Ukacha21/welstech/CAD/demo_big esp/61HXYjyJ1OL._AC_SL1001_.jpg

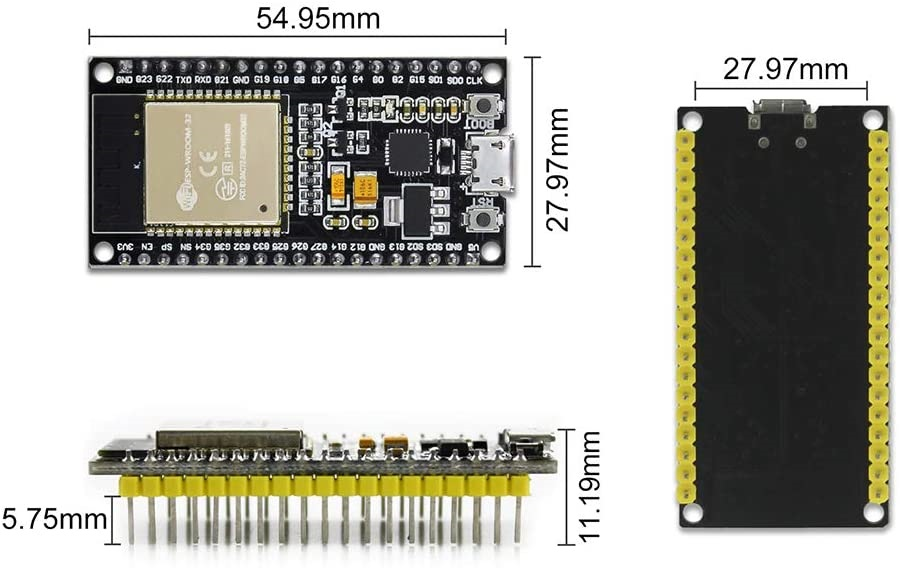
CAD/demo_big esp/61HXYjyJ1OL._AC_SL1001_.jpg
