Ukacha21/welstech/CAD/demo_big esp/bd75cf8a918120651273d0a94ace47d1c933943b_2_1024x606.png

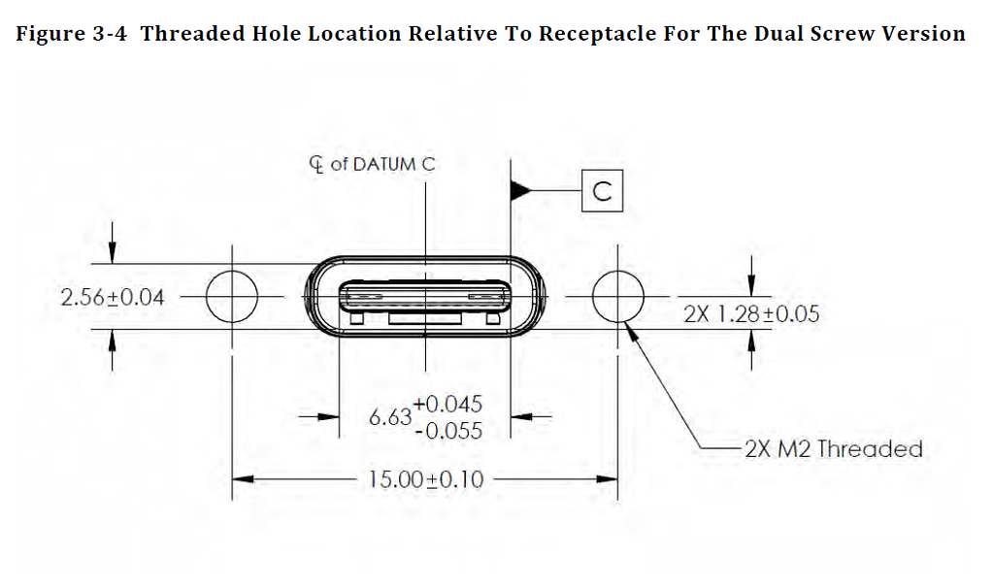
CAD/demo_big esp/bd75cf8a918120651273d0a94ace47d1c933943b_2_1024x606.png
