Ukacha21/welstech/CAD/demo_big esp/buttons3.jpg

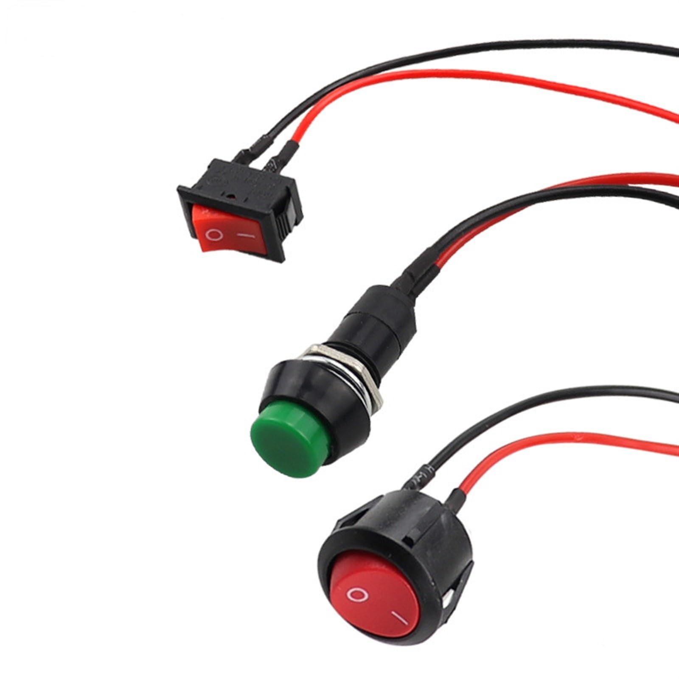
CAD/demo_big esp/buttons3.jpg
