Ukacha21/welstech/CAD/demo_big esp/buttons.png

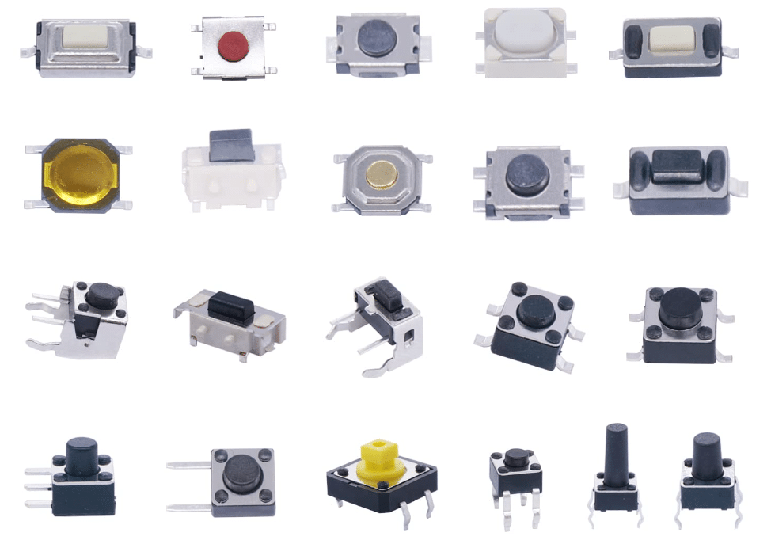
CAD/demo_big esp/buttons.png
