Ukacha21/welstech/CAD/demo_big esp/esp32 hd image.jpg

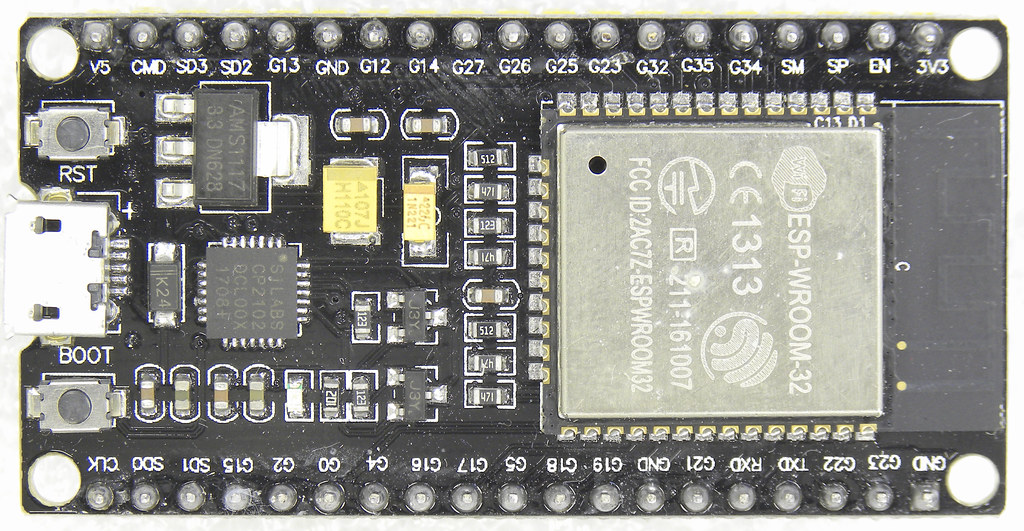
CAD/demo_big esp/esp32 hd image.jpg
