Ukacha21/welstech/CAD/demo_big esp/PAN-USB-C-SL-DIM1-500x500.webp

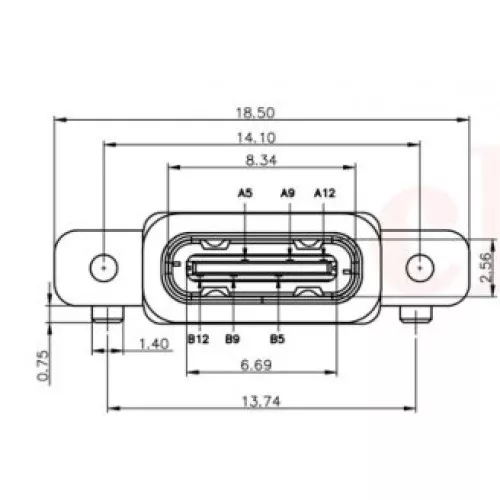
CAD/demo_big esp/PAN-USB-C-SL-DIM1-500x500.webp
