Ukacha21/welstech/Code/bpm formula.png

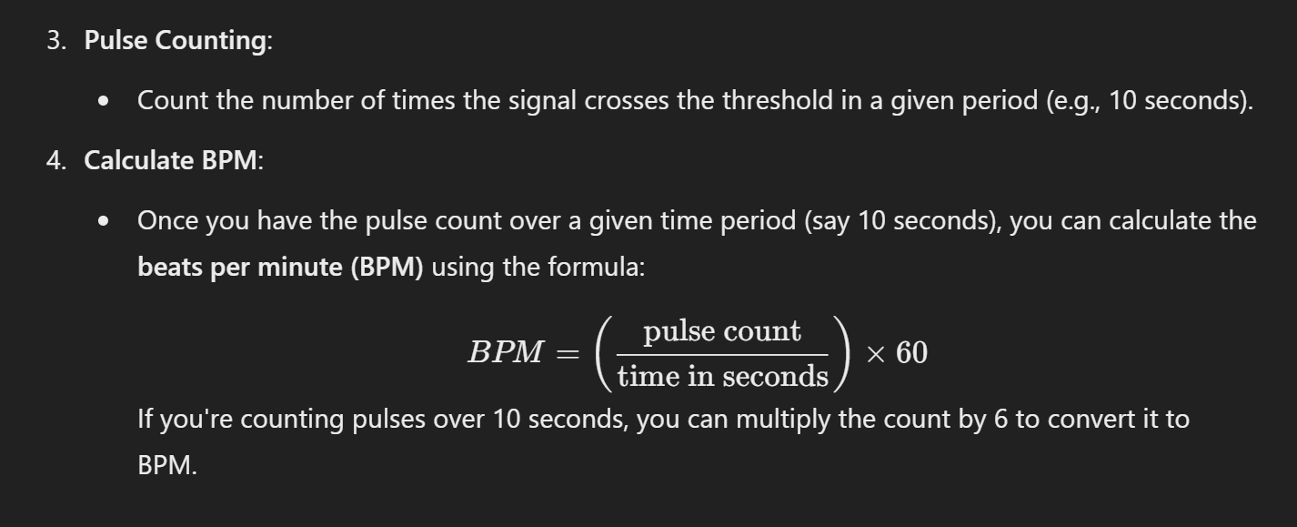
Code/bpm formula.png
