Ukacha21/welstech/Code/COM PORT name.png

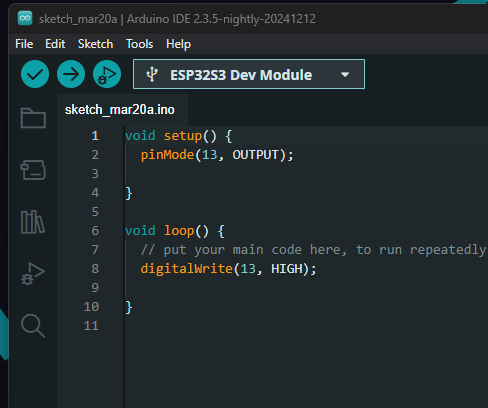
Code/COM PORT name.png
