Ukacha21/welstech/Schemaatics/BACKG.jpg

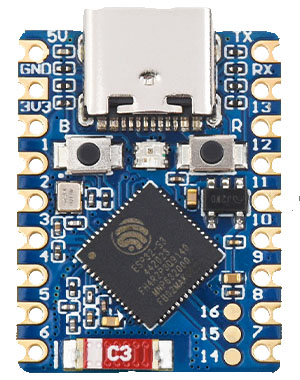
Schemaatics/BACKG.jpg
