Ukacha21/welstech/Schemaatics/breadboard dimensions.webp

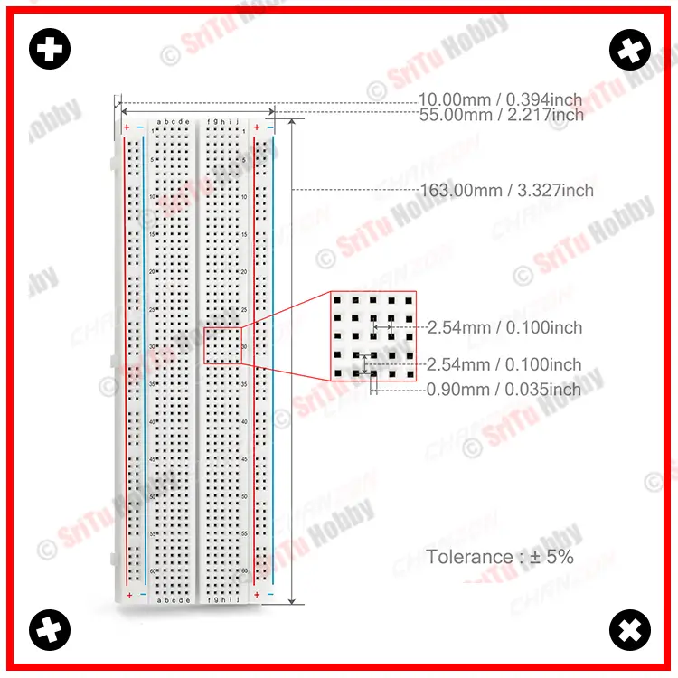
Schemaatics/breadboard dimensions.webp
