Ukacha21/welstech/Schemaatics/esp32-s3-mini-from-3-3v-source-v0-9cdqbcgkuqyc1.png

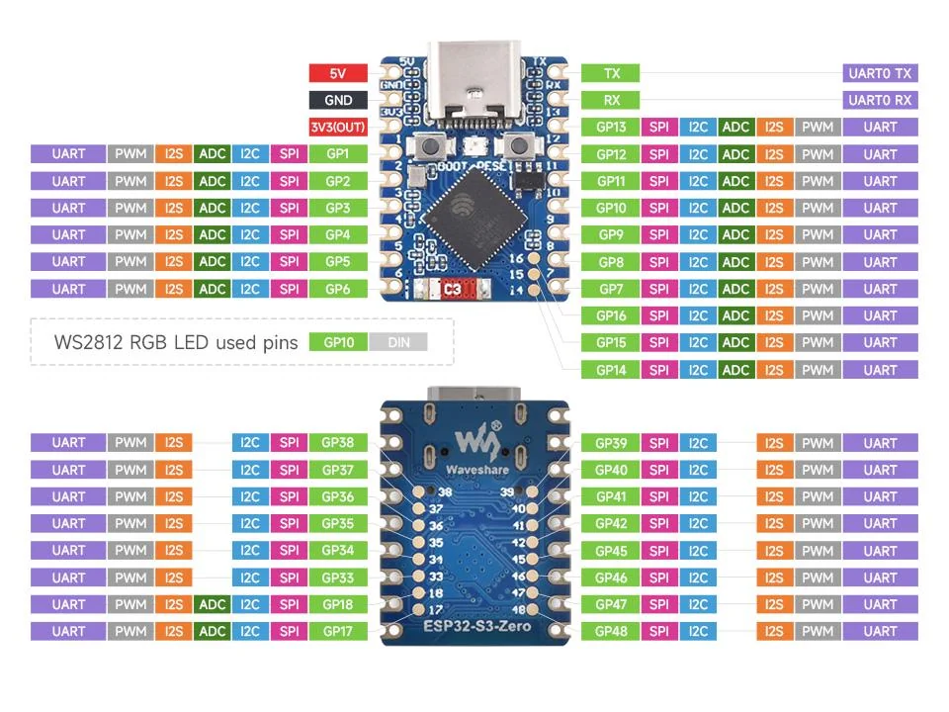
Schemaatics/esp32-s3-mini-from-3-3v-source-v0-9cdqbcgkuqyc1.png
