Ukacha21/welstech/Schemaatics/pressbutton without resistor.png

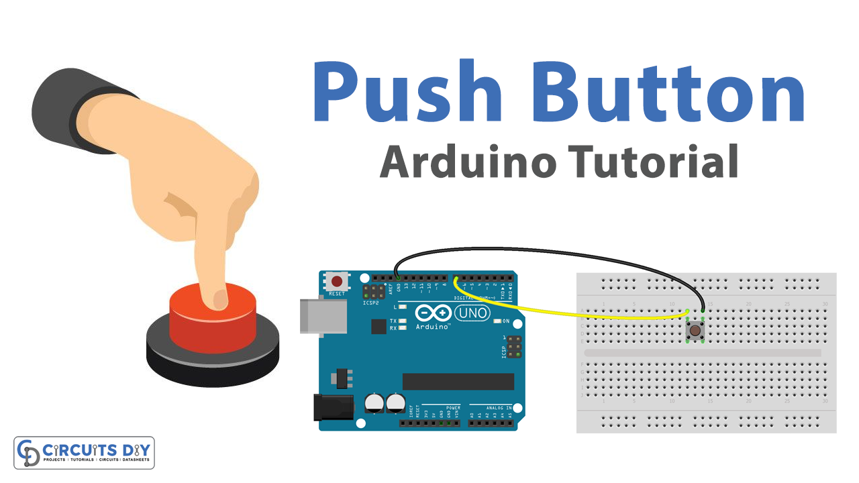
Schemaatics/pressbutton without resistor.png
