Ukacha21/welstech/welstech Mobile/regenerate missing filees or directories.jpg

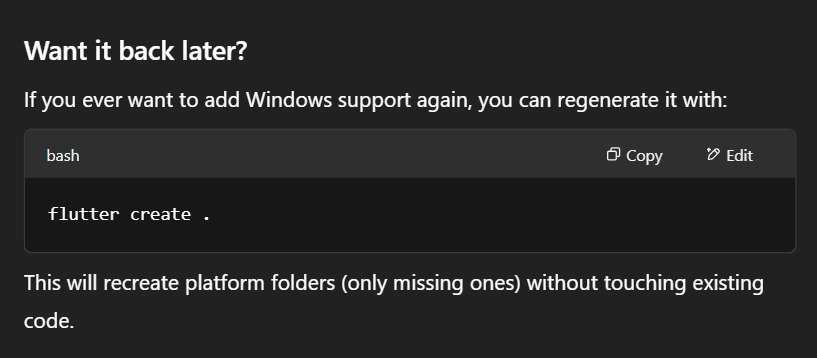
welstech Mobile/regenerate missing filees or directories.jpg
