Ukacha21/welstech/CAD/s3 casing/top - Copy (2).SLDPRT

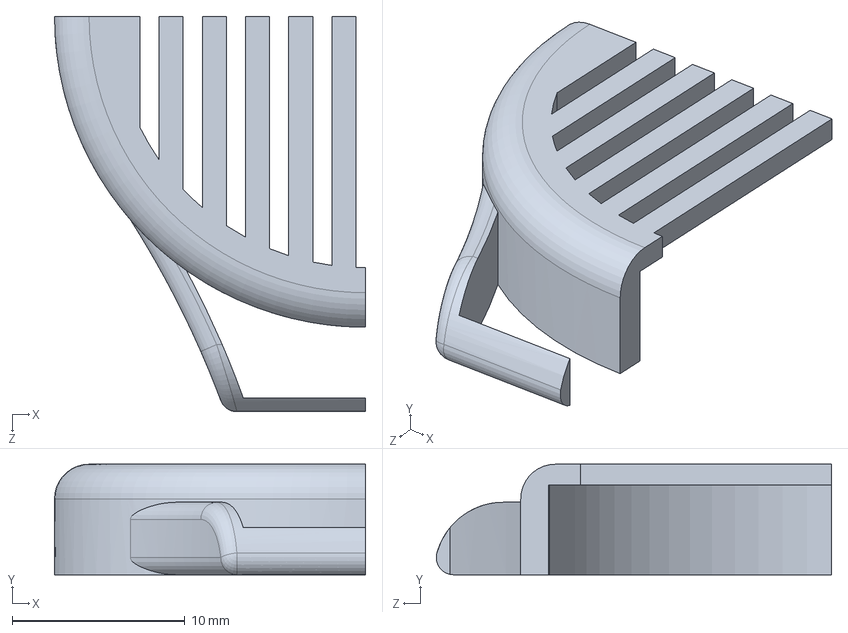
[picture p60: CAD file, 2025-05-14, an earlier design]
CAD/s3 casing/top - Copy (2).SLDPRT
18.0 x 6.40 x 22.9 mm
