Ukacha21/welstech/CAD/s3 casing/top - Copy - Copy.SLDPRT

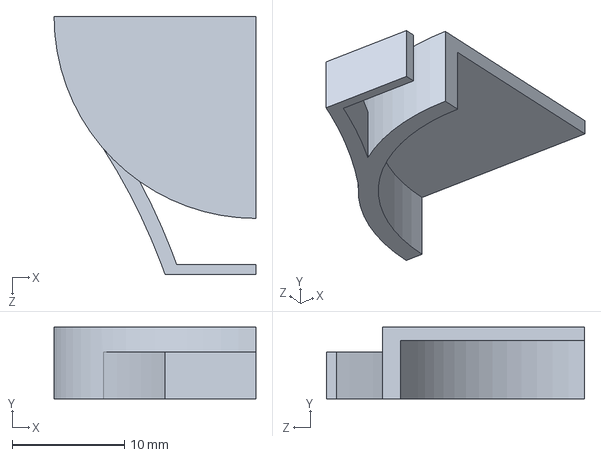
[picture p61: CAD file, 2025-05-14, an earlier design]
CAD/s3 casing/top - Copy - Copy.SLDPRT
18.0 x 6.40 x 23.0 mm
