Ukacha21/welstech/CAD/s3 casing/Demo/base without lcd - Copy.SLDPRT

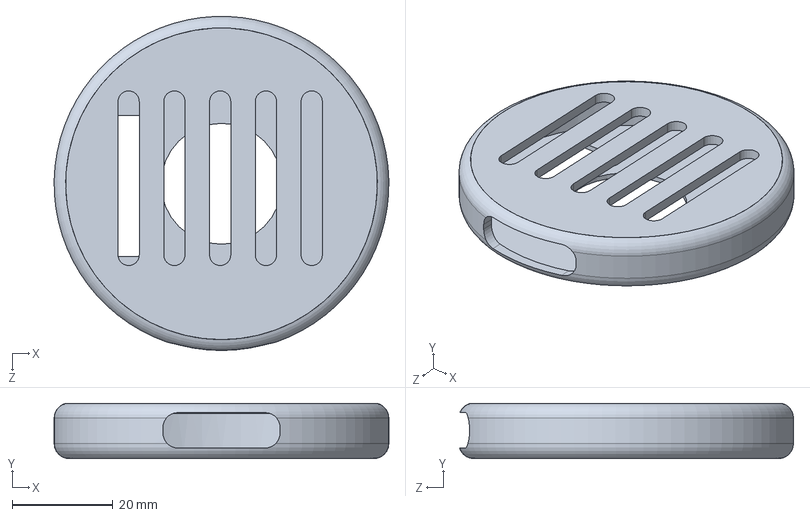
[picture p62: CAD file, 2025-05-14, an earlier design]
CAD/s3 casing/Demo/base without lcd - Copy.SLDPRT
66.6 x 11.0 x 66.4 mm
